vikamuhan-reddy/Kishan_Netra/ai/dataset_split/val/Bacterial Blight/field_0000.jpg

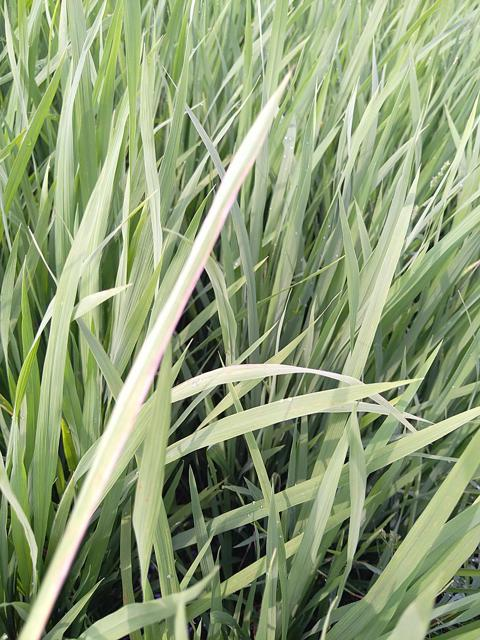
ai/dataset_split/val/Bacterial Blight/field_0000.jpg
