vikamuhan-reddy/Kishan_Netra/ai/dataset_split/val/Bacterial Blight/field_0005.jpg

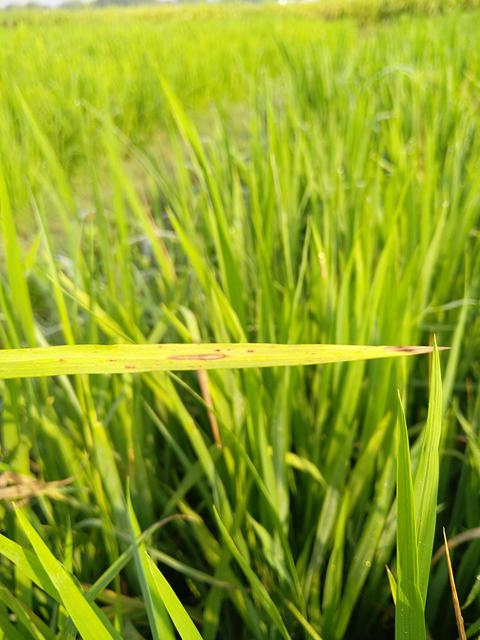
ai/dataset_split/val/Bacterial Blight/field_0005.jpg
