vikamuhan-reddy/Kishan_Netra/ai/dataset_split/val/Bacterial Blight/field_0006.jpg

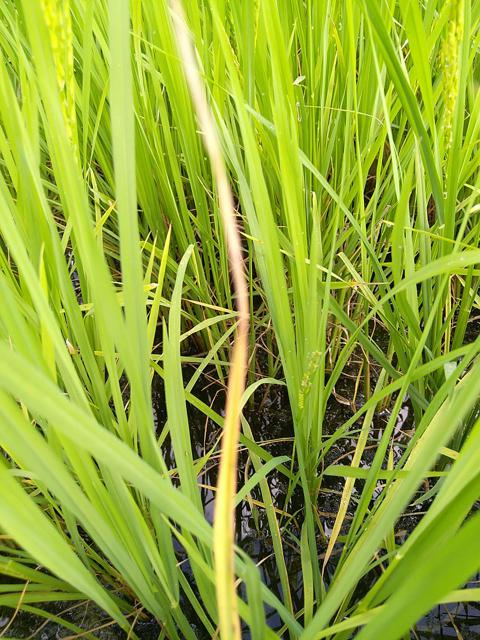
ai/dataset_split/val/Bacterial Blight/field_0006.jpg
