vikamuhan-reddy/Kishan_Netra/ai/dataset_split/val/Bacterial Blight/field_0016.jpg

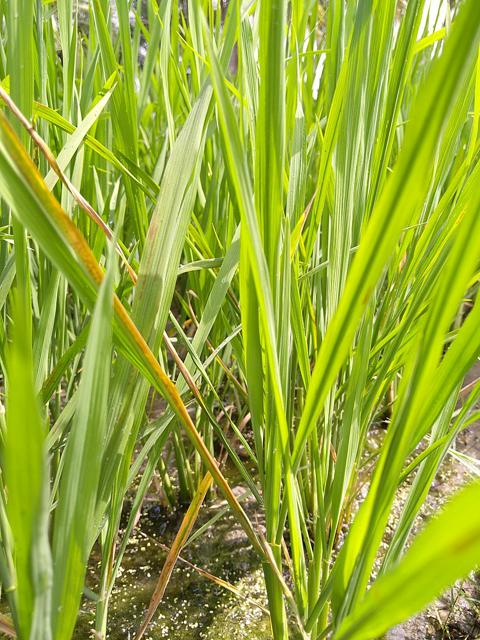
ai/dataset_split/val/Bacterial Blight/field_0016.jpg
