vikamuhan-reddy/Kishan_Netra/ai/dataset_split/val/Bacterial Blight/field_0022.jpg

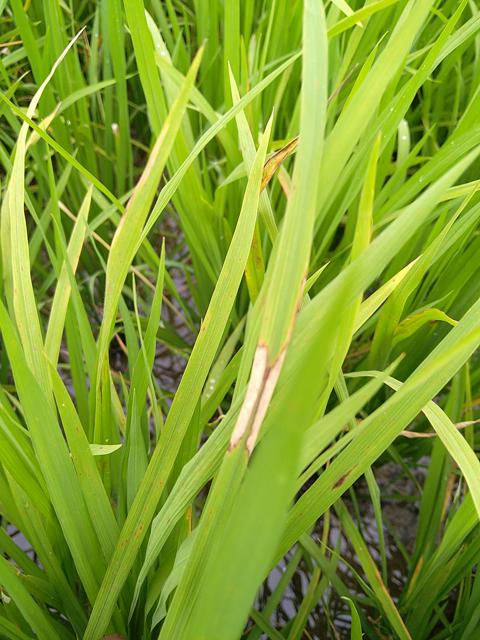
ai/dataset_split/val/Bacterial Blight/field_0022.jpg
