vikamuhan-reddy/Kishan_Netra/ai/dataset_split/val/Bacterial Blight/field_0034.jpg

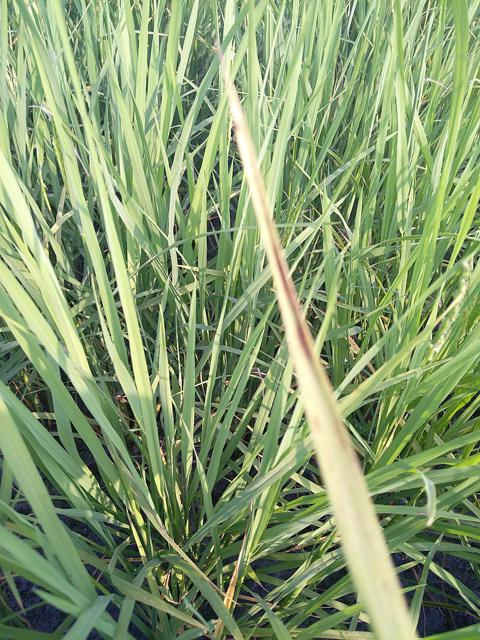
ai/dataset_split/val/Bacterial Blight/field_0034.jpg
