vikamuhan-reddy/Kishan_Netra/ai/dataset_split/val/Bacterial Blight/field_0042.jpg

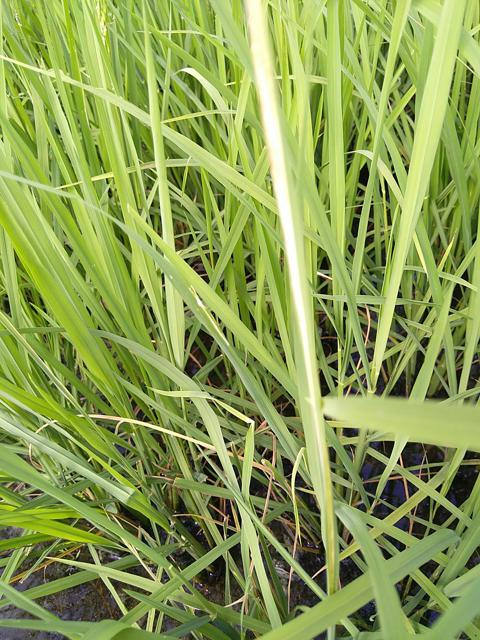
ai/dataset_split/val/Bacterial Blight/field_0042.jpg
