vikamuhan-reddy/Kishan_Netra/ai/dataset_split/val/Bacterial Blight/field_0058.jpg

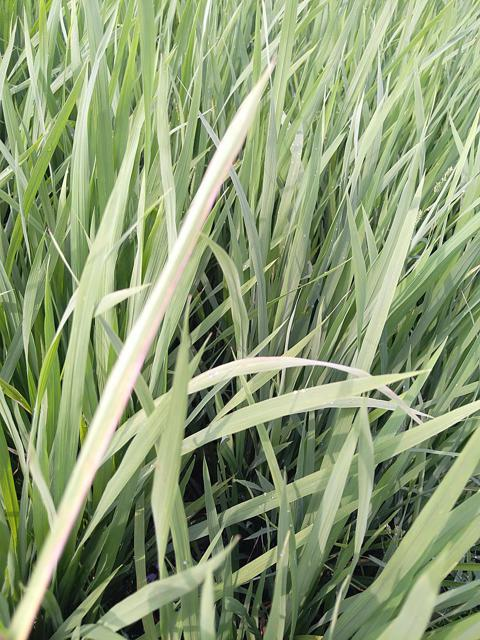
ai/dataset_split/val/Bacterial Blight/field_0058.jpg
