vikamuhan-reddy/Kishan_Netra/ai/dataset_split/val/Bacterial Blight/field_0060.jpg

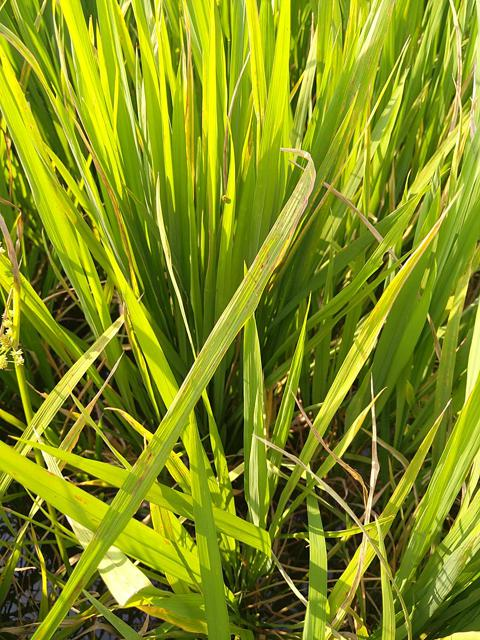
ai/dataset_split/val/Bacterial Blight/field_0060.jpg
