vikamuhan-reddy/Kishan_Netra/ai/dataset_split/val/Bacterial Blight/field_0063.jpg

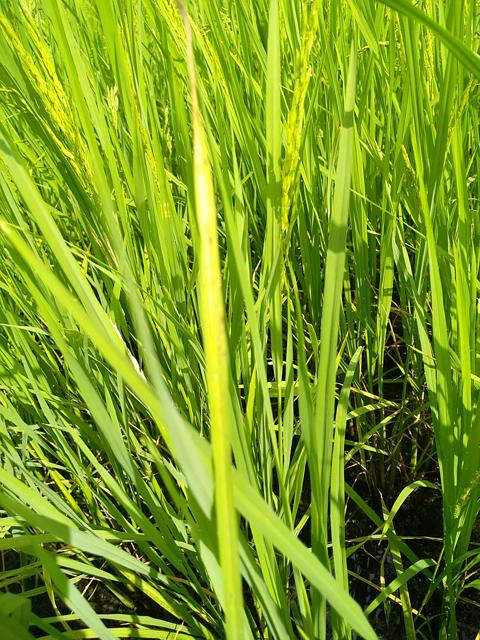
ai/dataset_split/val/Bacterial Blight/field_0063.jpg
