vikamuhan-reddy/Kishan_Netra/ai/dataset_split/val/Bacterial Blight/field_0064.jpg

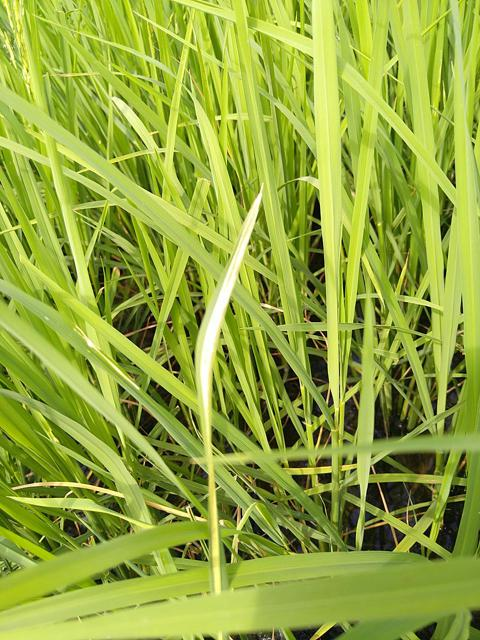
ai/dataset_split/val/Bacterial Blight/field_0064.jpg
