vikamuhan-reddy/Kishan_Netra/ai/dataset_split/val/Bacterial Blight/lab_0012.jpg

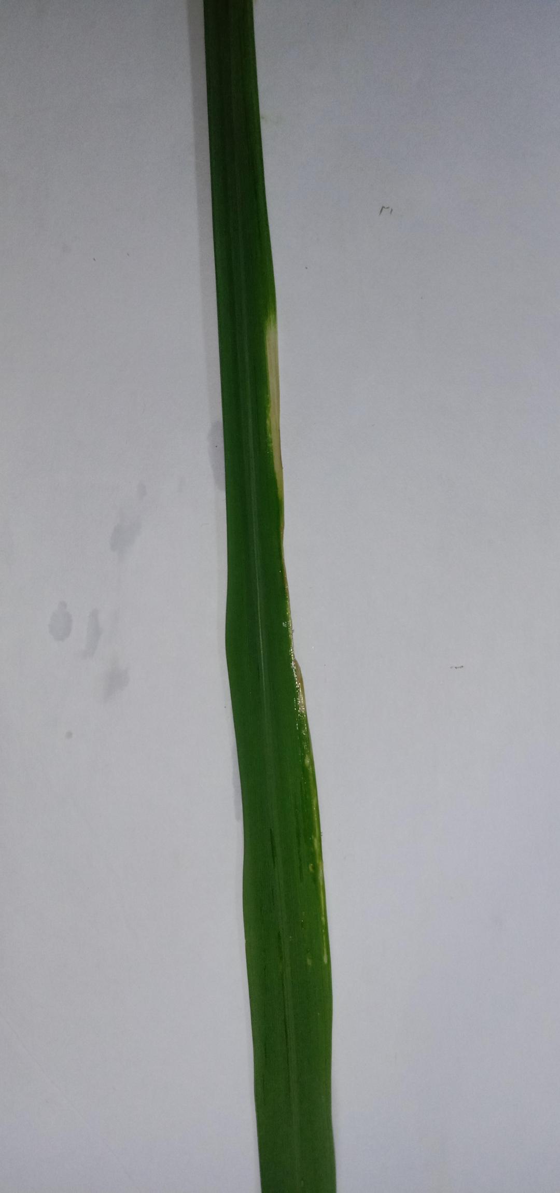
ai/dataset_split/val/Bacterial Blight/lab_0012.jpg
