vikamuhan-reddy/Kishan_Netra/ai/dataset_split/val/Bacterial Blight/lab_0023.jpg

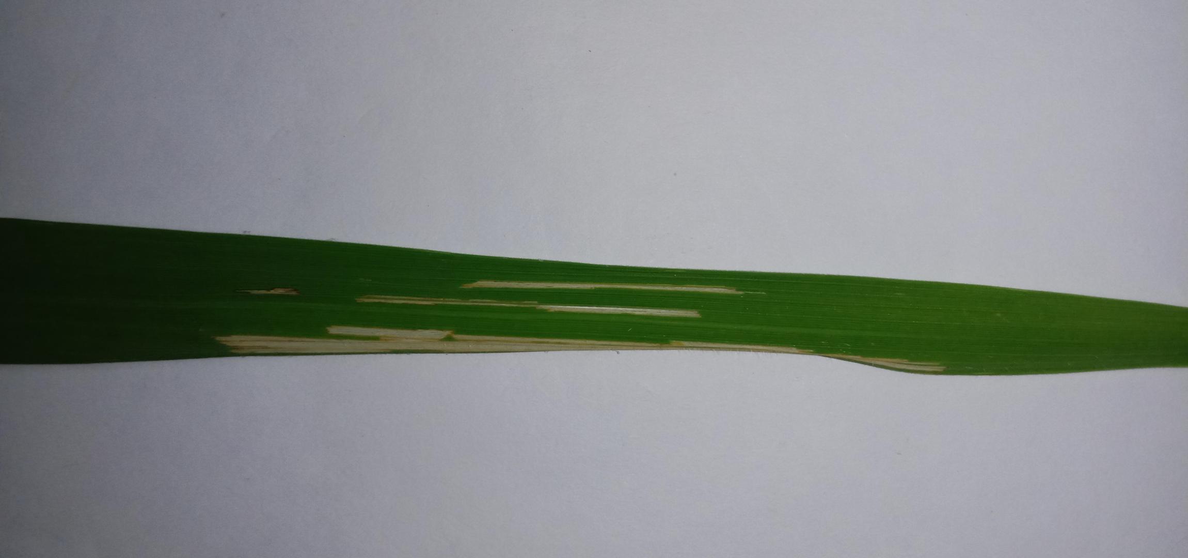
ai/dataset_split/val/Bacterial Blight/lab_0023.jpg
