vikamuhan-reddy/Kishan_Netra/ai/dataset_split/val/Bacterial Blight/lab_0028.jpg

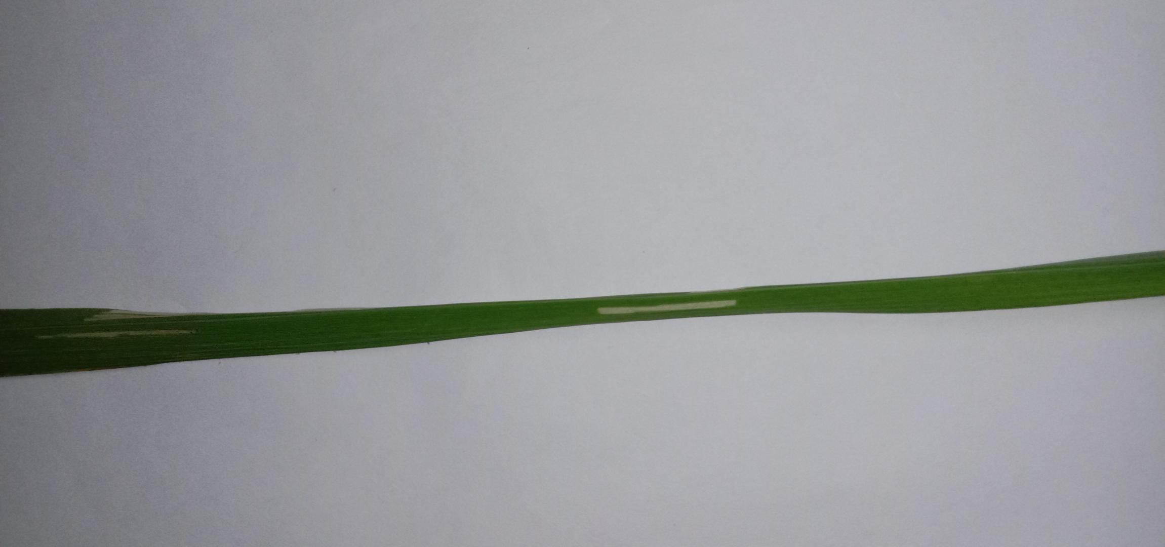
ai/dataset_split/val/Bacterial Blight/lab_0028.jpg
