vikamuhan-reddy/Kishan_Netra/ai/dataset_split/val/Bacterial Blight/lab_0031.jpg

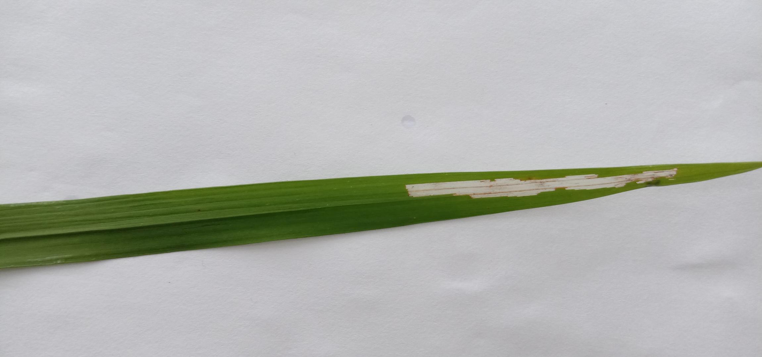
ai/dataset_split/val/Bacterial Blight/lab_0031.jpg
