vikamuhan-reddy/Kishan_Netra/hardware/cad/product_field.png

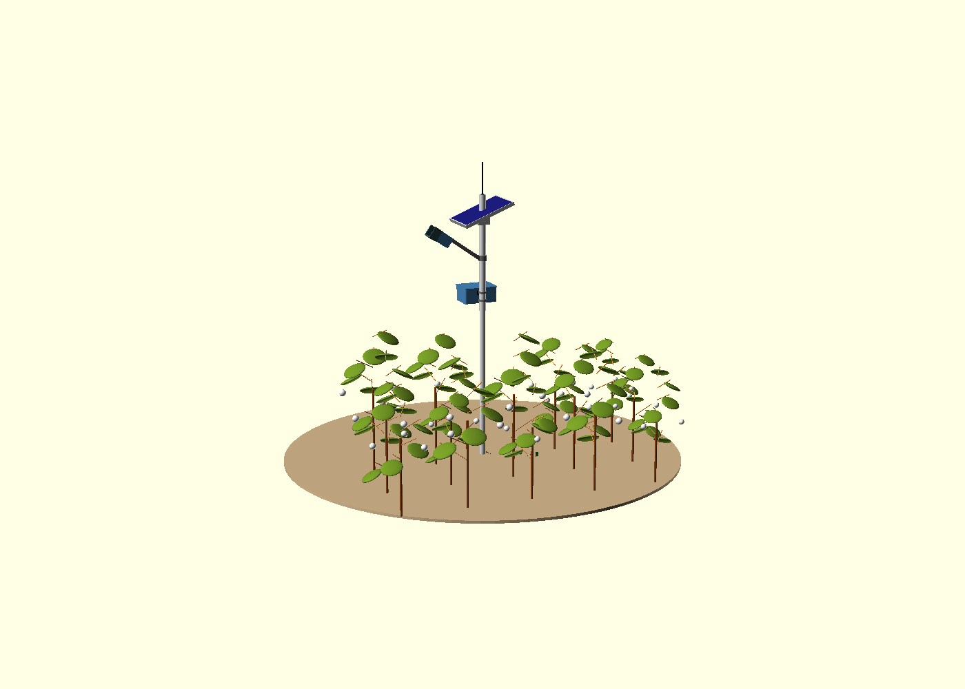
hardware/cad/product_field.png
