vikamuhan-reddy/Kishan_Netra/hardware/cad/product_station.png

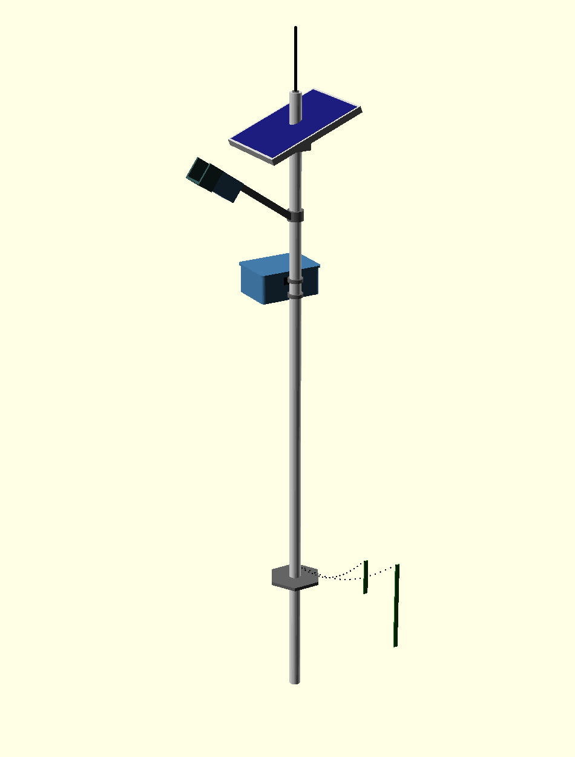
hardware/cad/product_station.png
