vikamuhan-reddy/Kishan_Netra/hardware/cad/render_exploded.png

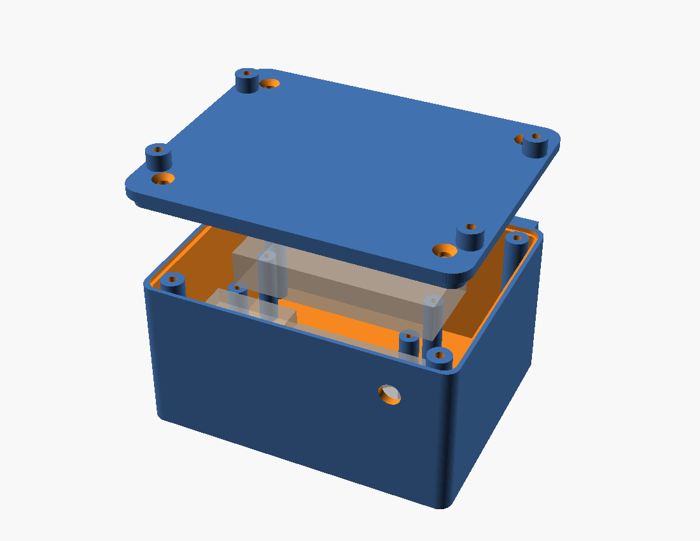
hardware/cad/render_exploded.png
