vikamuhan-reddy/Kishan_Netra/ai/dataset_split/test/Bacterial Blight/field_0002.jpg

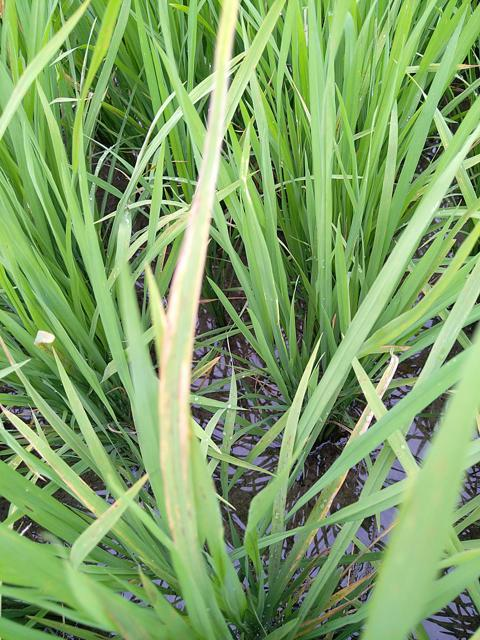
ai/dataset_split/test/Bacterial Blight/field_0002.jpg
