vikamuhan-reddy/Kishan_Netra/ai/dataset_split/test/Bacterial Blight/field_0012.jpg

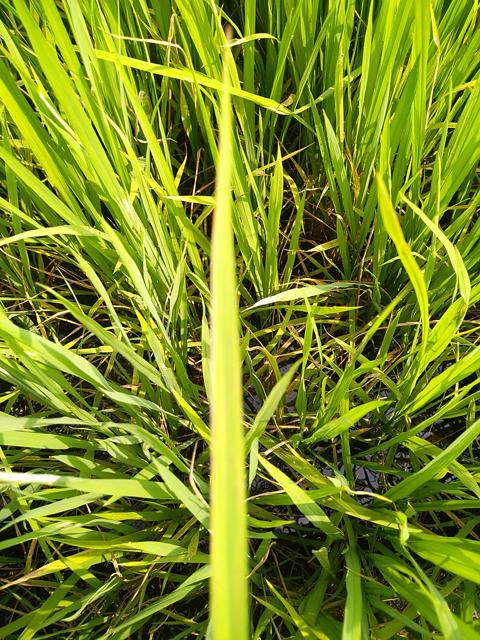
ai/dataset_split/test/Bacterial Blight/field_0012.jpg
