vikamuhan-reddy/Kishan_Netra/ai/dataset_split/test/Bacterial Blight/field_0022.jpg

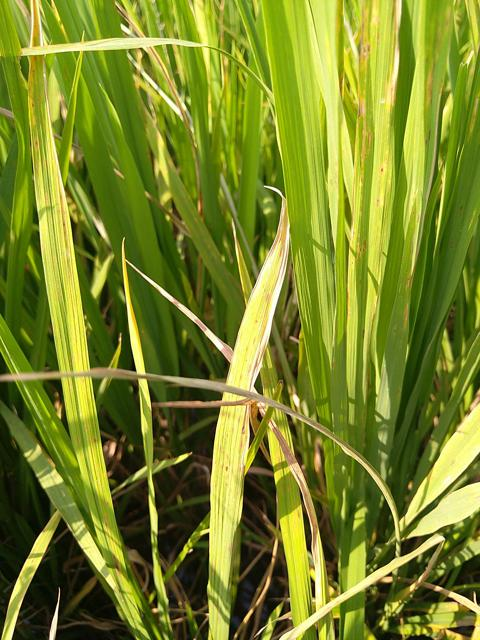
ai/dataset_split/test/Bacterial Blight/field_0022.jpg
