vikamuhan-reddy/Kishan_Netra/ai/dataset_split/test/Bacterial Blight/field_0036.jpg

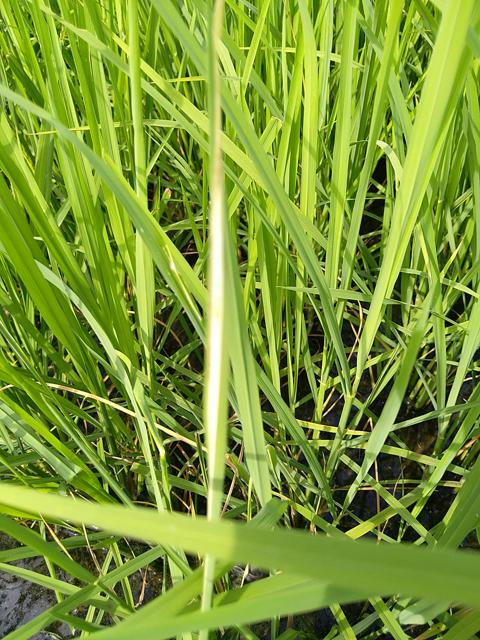
ai/dataset_split/test/Bacterial Blight/field_0036.jpg
