vikamuhan-reddy/Kishan_Netra/ai/dataset_split/test/Bacterial Blight/field_0044.jpg

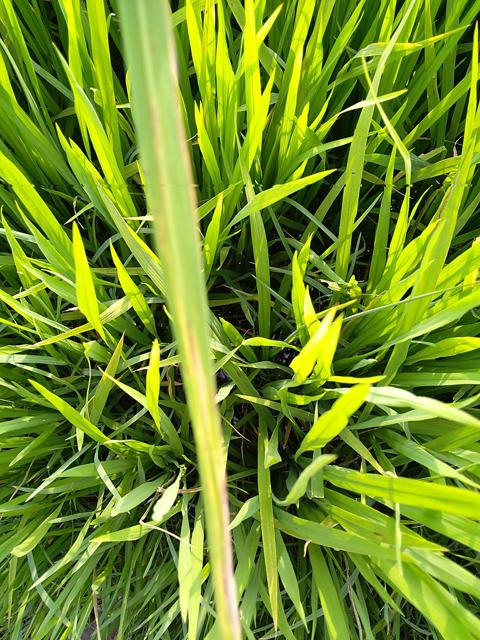
ai/dataset_split/test/Bacterial Blight/field_0044.jpg
