vikamuhan-reddy/Kishan_Netra/ai/dataset_split/test/Bacterial Blight/field_0053.jpg

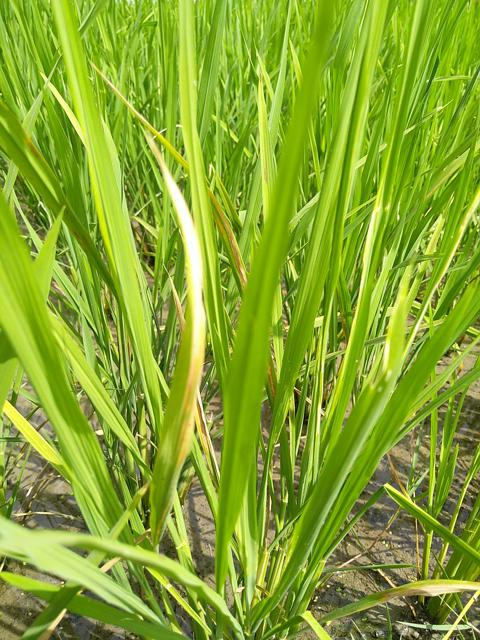
ai/dataset_split/test/Bacterial Blight/field_0053.jpg
