vikamuhan-reddy/Kishan_Netra/ai/dataset_split/test/Bacterial Blight/field_0054.jpg

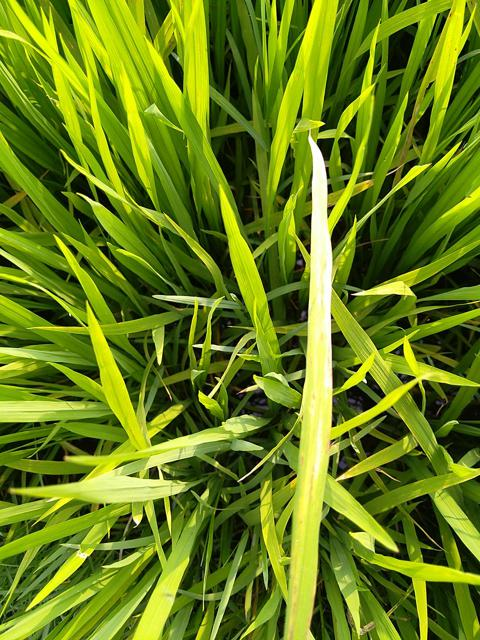
ai/dataset_split/test/Bacterial Blight/field_0054.jpg
