vikamuhan-reddy/Kishan_Netra/ai/dataset_split/test/Bacterial Blight/field_0058.jpg

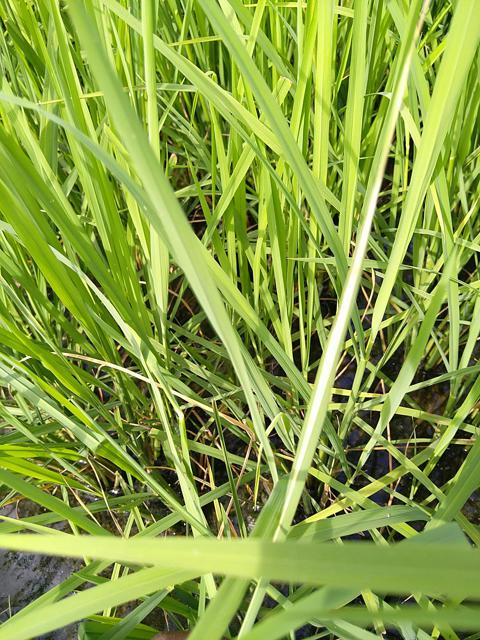
ai/dataset_split/test/Bacterial Blight/field_0058.jpg
