vikamuhan-reddy/Kishan_Netra/ai/dataset_split/test/Bacterial Blight/field_0060.jpg

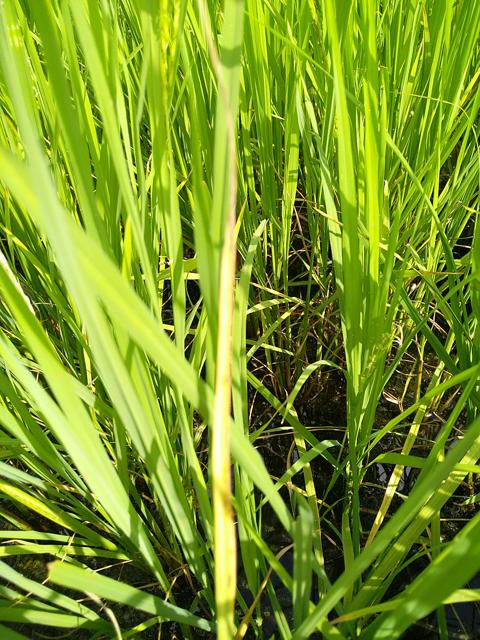
ai/dataset_split/test/Bacterial Blight/field_0060.jpg
