vikamuhan-reddy/Kishan_Netra/ai/dataset_split/test/Bacterial Blight/field_0062.jpg

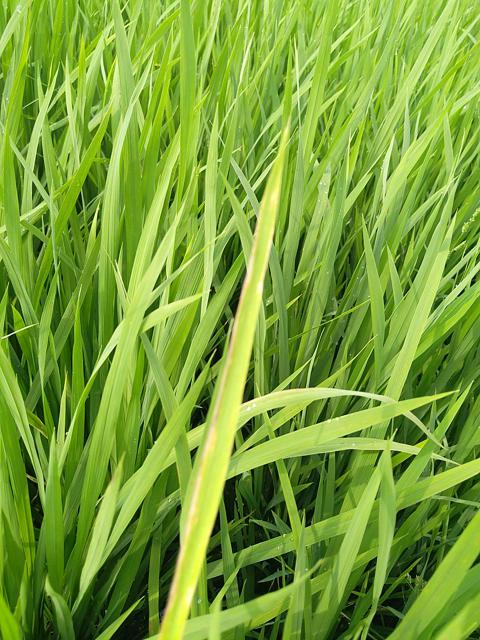
ai/dataset_split/test/Bacterial Blight/field_0062.jpg
