vikamuhan-reddy/Kishan_Netra/ai/dataset_split/test/Bacterial Blight/lab_0002.jpg

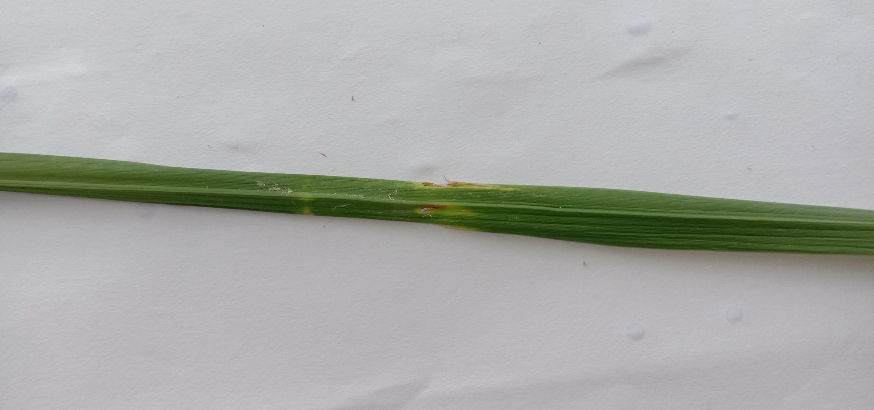
ai/dataset_split/test/Bacterial Blight/lab_0002.jpg
