vikamuhan-reddy/Kishan_Netra/ai/dataset_split/test/Bacterial Blight/lab_0014.jpg

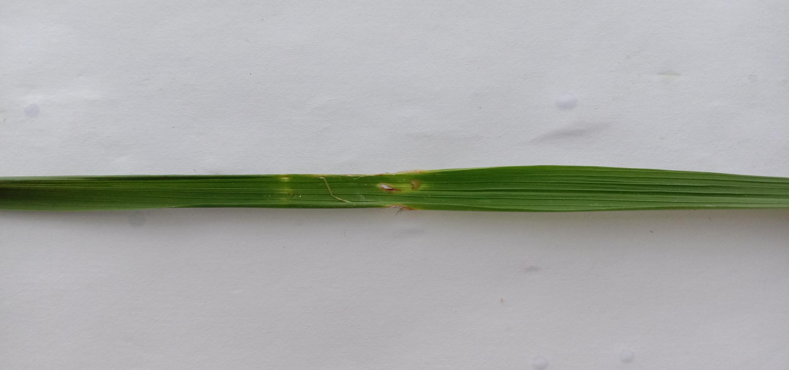
ai/dataset_split/test/Bacterial Blight/lab_0014.jpg
