vikamuhan-reddy/Kishan_Netra/ai/dataset_split/test/Bacterial Blight/lab_0023.jpg

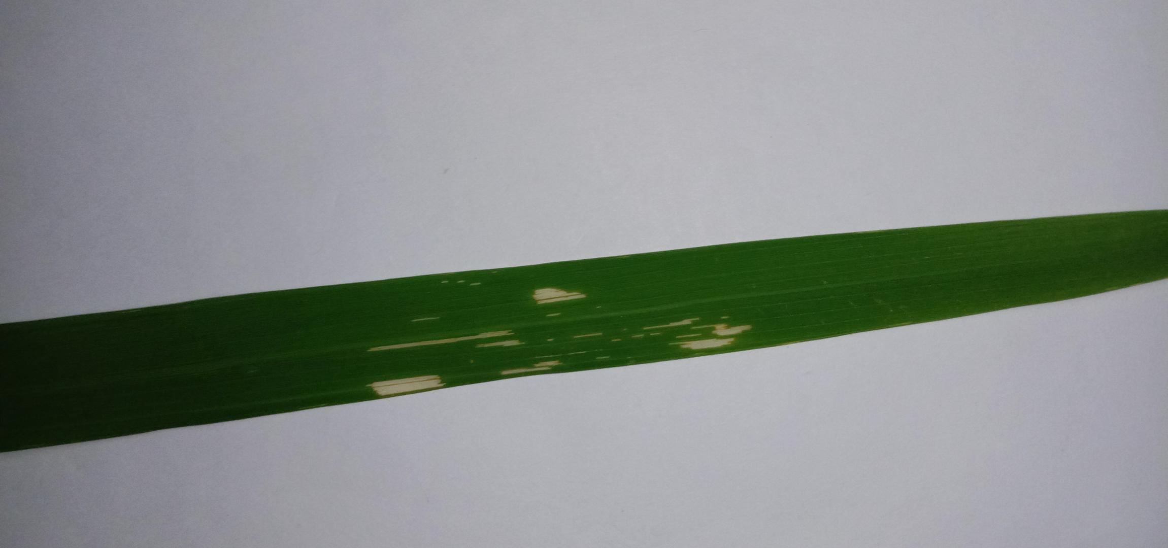
ai/dataset_split/test/Bacterial Blight/lab_0023.jpg
