vikamuhan-reddy/Kishan_Netra/ai/dataset_split/test/Bacterial Blight/lab_0027.jpg

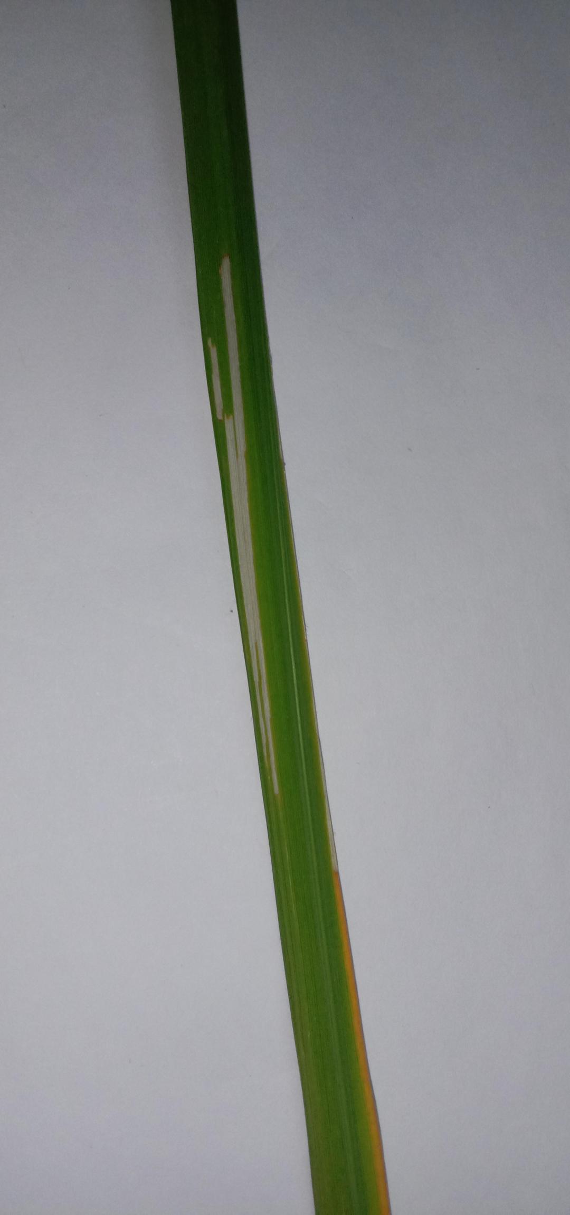
ai/dataset_split/test/Bacterial Blight/lab_0027.jpg
