vikamuhan-reddy/Kishan_Netra/ai/dataset_split/test/Bacterial Blight/lab_0030.jpg

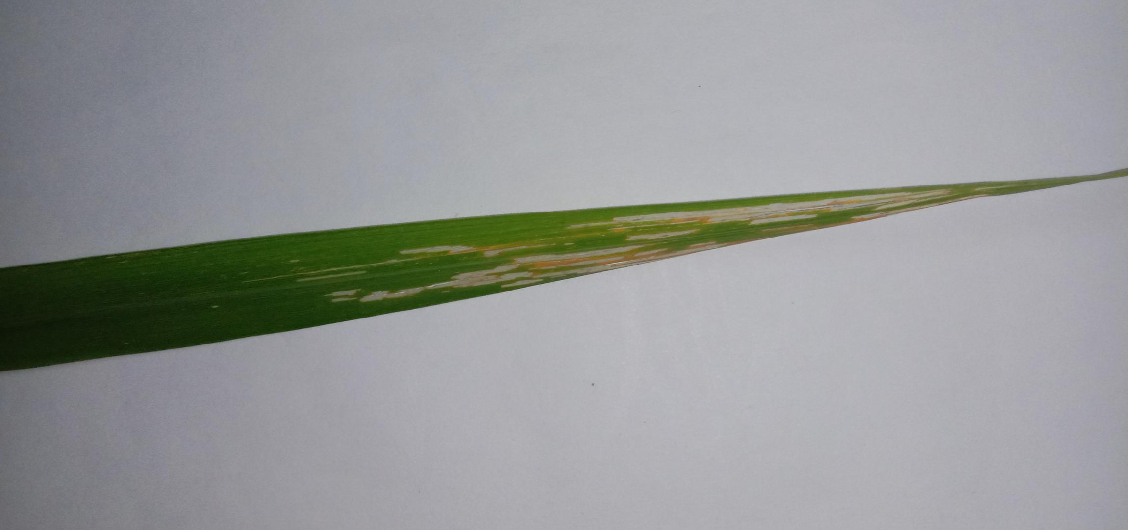
ai/dataset_split/test/Bacterial Blight/lab_0030.jpg
